hipe-0/VausGamingPaddle/Gerber/2024-09-23 Vaus Gaming paddle shematic v1.02_etch_silk_top.pdf

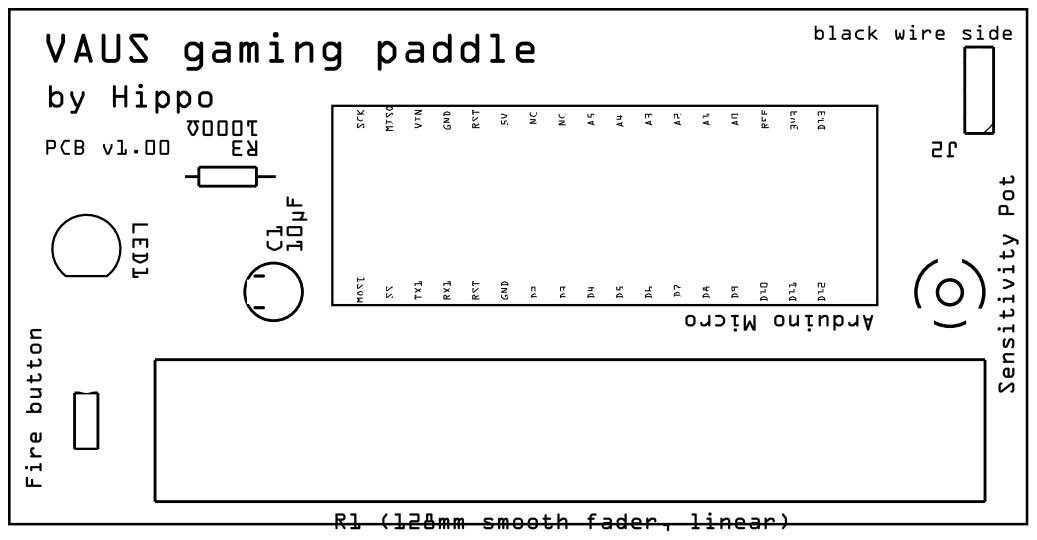
[picture p19: page 1]
