hipe-0/VausGamingPaddle/Gerber/2024-09-23 Vaus Gaming paddle shematic v1.02_etch_silk_top_mirror.pdf

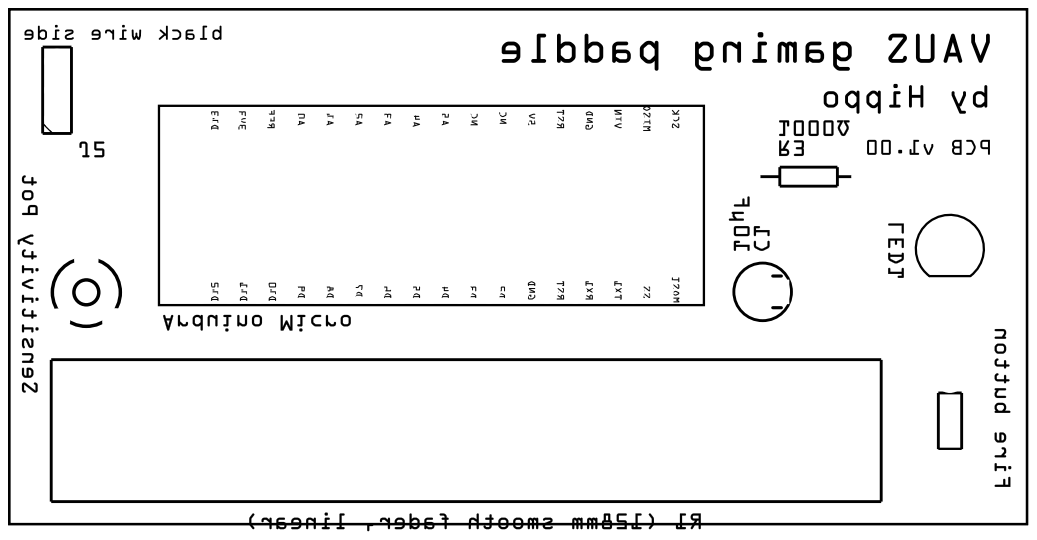
[picture p20: page 1]
