hipe-0/VausGamingPaddle/20240102_194252.jpg

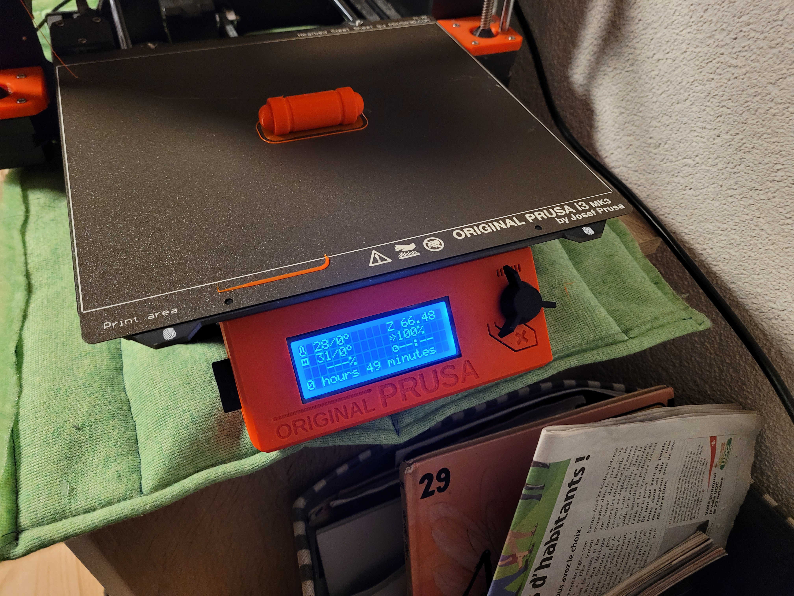
20240102_194252.jpg
