hipe-0/VausGamingPaddle/20240919_225709.jpg

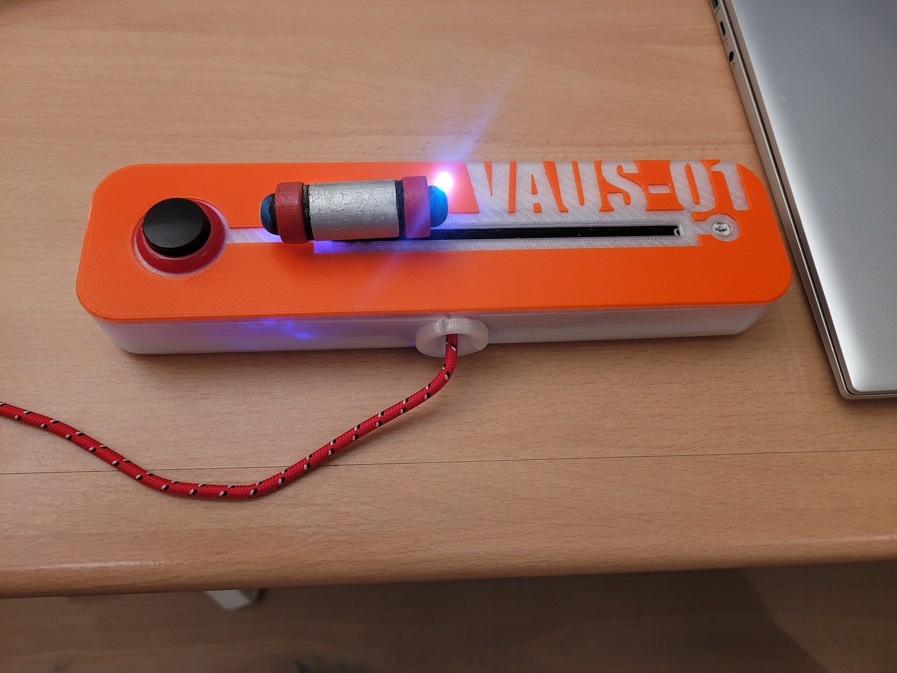
20240919_225709.jpg
