hipe-0/VausGamingPaddle/20240919_225710.jpg

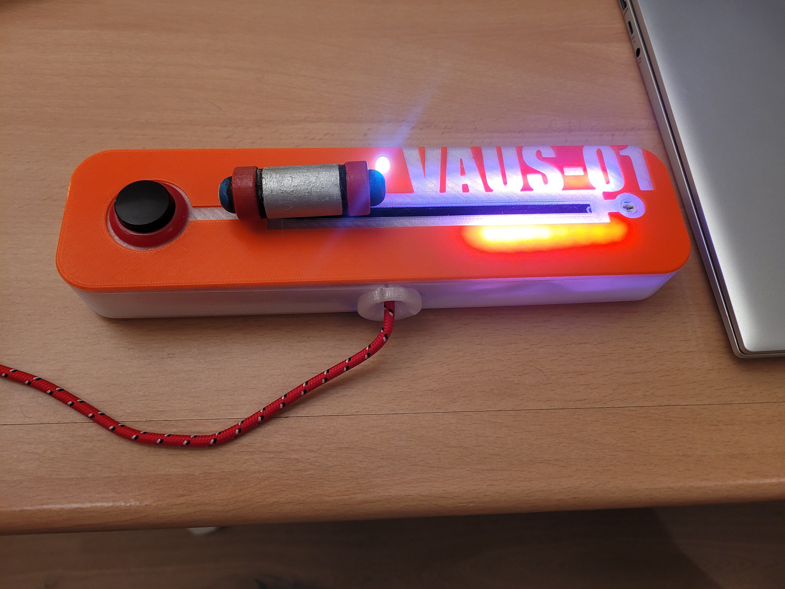
20240919_225710.jpg
